Ketturi/LedMatrix/Hardware/Case/IMG_20160126_170815.jpg

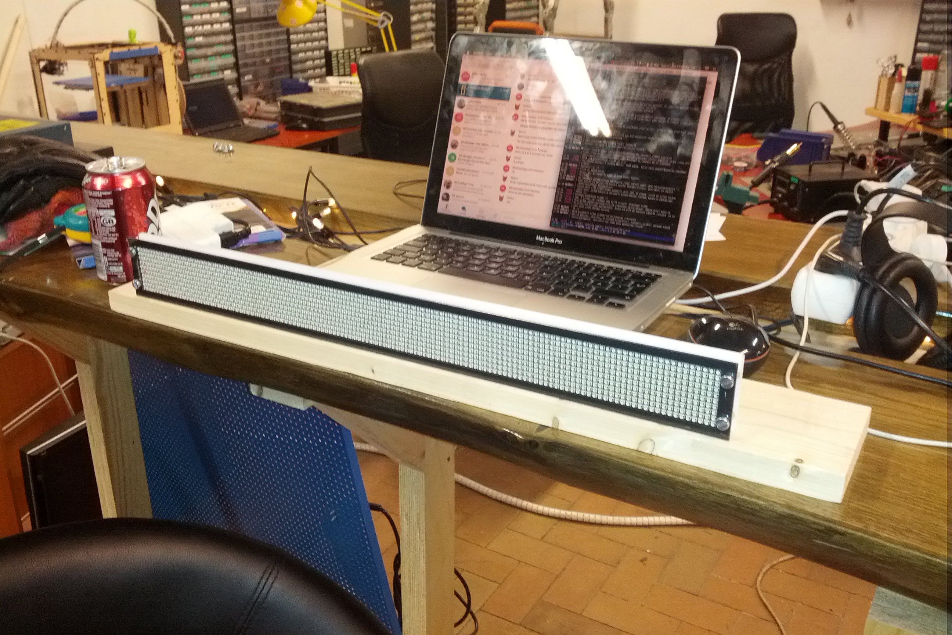
Hardware/Case/IMG_20160126_170815.jpg
