Ketturi/LedMatrix/Hardware/Case/IMG_20160127_182910.jpg

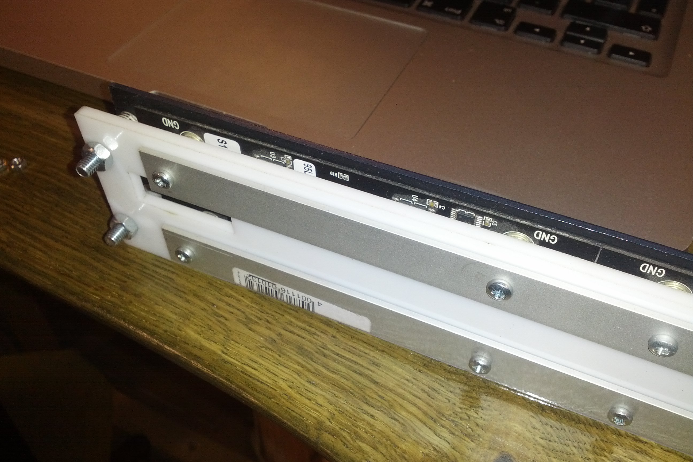
Hardware/Case/IMG_20160127_182910.jpg
