Ketturi/LedMatrix/Hardware/IMG_20160901_110750.jpg

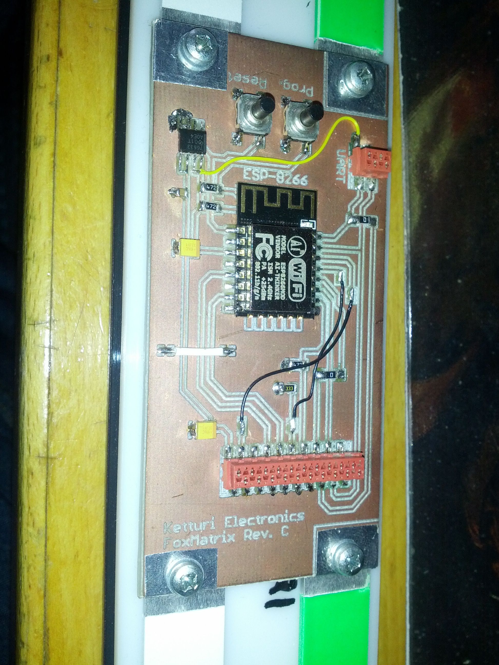
Hardware/IMG_20160901_110750.jpg
