Ketturi/LedMatrix/Arduino source/FoxFont.h

/*
  10 pixels high variable width font for LED matrix display
  created by
  Ketturi Fox 2017

  This work is licensed under a Creative Commons Attribution-ShareAlike 4.0 International License.
  https://creativecommons.org/licenses/by-sa/4.0/
*/

const uint8_t FoxFontBitmaps[] PROGMEM = {
  // Bitmap Data:

  /* 0x20 032 */
  0x80, 0x80, 0x80, 0x80, 0x80, 0x80, 0x00, 0x80, /* 0x21 033 */
  0x90, 0x90, 0x90, /* 0x22 034 */
  0x48, 0x48, 0xFC, 0x48, 0x48, 0xFC, 0x48, 0x48, /* 0x23 035 */
  0x20, 0x70, 0x88, 0x80, 0x70, 0x08, 0x88, 0x70, 0x20, /* 0x24 036 */
  0x42, 0xA4, 0x48, 0x10, 0x24, 0x4A, 0x84, /* 0x25 037 */
  0x30, 0x48, 0x30, 0x4C, 0x88, 0x88, 0x74, /* 0x26 038 */
  0x40, 0x40, 0x80, /* 0x27 039 */
  0x20, 0x40, 0x80, 0x80, 0x80, 0x80, 0x80, 0x80, 0x40, 0x20, /* 0x28 040 */
  0x80, 0x40, 0x20, 0x20, 0x20, 0x20, 0x20, 0x20, 0x40, 0x80, /* 0x29 041 */
  0xA8, 0x70, 0xF8, 0x70, 0xA8, /* 0x2A 042 */
  0x20, 0x20, 0xF8, 0x20, 0x20, /* 0x2B 043 */
  0x40, 0x80, /* 0x2C 044 */
  0xF8, /* 0x2D 045 */
  0x80, /* 0x2E 046 */
  0x04, 0x08, 0x10, 0x20, 0x40, 0x80, /* 0x2F 047 */
  0x70, 0x88, 0x88, 0x88, 0x88, 0x88, 0x88, 0x70, /* 0x30 048 */
  0x40, 0xC0, 0x40, 0x40, 0x40, 0x40, 0x40, 0xE0, /* 0x31 049 */
  0x70, 0x88, 0x08, 0x10, 0x20, 0x40, 0x80, 0xF8, /* 0x32 050 */
  0x70, 0x88, 0x08, 0x30, 0x08, 0x08, 0x88, 0x70, /* 0x33 051 */
  0x08, 0x18, 0x28, 0x48, 0x88, 0xF8, 0x08, 0x08, /* 0x34 052 */
  0xF8, 0x80, 0x80, 0xF0, 0x08, 0x08, 0x88, 0x70, /* 0x35 053 */
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
  { 243, 8, 8, 6, 0, -8 }, /* 0x45 069 */
  { 251, 8, 8, 6, 0, -8 }, /* 0x46 070 */
  { 259, 8, 8, 6, 0, -8 }, /* 0x47 071 */
  { 267, 8, 8, 6, 0, -8 }, /* 0x48 072 */
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
};


const GFXfont FoxFont PROGMEM = {
  (uint8_t  *)FoxFontBitmaps,
  (GFXglyph *)FoxFontGlyphs,
  0x20, 0x7E, 10
};
