Ketturi/LedMatrix/Arduino source/Bitmaps.h

/*
   Static bitmap icons in Adafruit GFX format
   Ketturi Fox 2017

  This work is licensed under a Creative Commons Attribution-ShareAlike 4.0 International License.
  https://creativecommons.org/licenses/by-sa/4.0/
*/
 
 // 'clock'
const unsigned char BitmapClock [] PROGMEM = {
  0x3e, 0x00, 0x41, 0x00, 0x82, 0x80, 0x84, 0x80, 0xb8, 0x80, 0x80, 0x80, 0x80, 0x80, 0x41, 0x00, 
  0x3e, 0x00, 0x00, 0x0
};
 // 'calendar'
const unsigned char BitmapCalendar [] PROGMEM = {
  0x63, 0x00, 0xff, 0x80, 0xff, 0x80, 0x80, 0x80, 0xaa, 0x80, 0x80, 0x80, 0xaa, 0x80, 0x80, 0x80, 
  0xff, 0x80, 0x00, 0x0
};
 // 'info'
const unsigned char BitmapInfo [] PROGMEM = {
  0x3e, 0x00, 0x41, 0x00, 0x88, 0x80, 0x80, 0x80, 0x88, 0x80, 0x88, 0x80, 0x88, 0x80, 0x41, 0x00, 
  0x3e, 0x00, 0x00, 0x0
};
 // 'guestion'
const unsigned char BitmapGuestion [] PROGMEM = {
  0x3e, 0x00, 0x41, 0x00, 0x9c, 0x80, 0x84, 0x80, 0x88, 0x80, 0x80, 0x80, 0x88, 0x80, 0x41, 0x00, 
  0x3e, 0x00, 0x00, 0x0
};
 // 'message'
const unsigned char BitmapMsg [] PROGMEM = {
  0x3e, 0x00, 0x41, 0x00, 0x80, 0x80, 0xaa, 0x80, 0x80, 0x80, 0x41, 0x00, 0x2e, 0x00, 0x30, 0x00, 
  0x20, 0x00, 0x00, 0x0
};
 // 'bus'
const unsigned char BitmapBus [] PROGMEM = {
  0x7f, 0x00, 0xbe, 0x80, 0x80, 0x80, 0x84, 0x80, 0x8e, 0x80, 0xff, 0x80, 0x9c, 0x80, 0xff, 0x80, 
  0x63, 0x00, 0x00, 0x0
};
 // 'email'
const unsigned char BitmapEmail [] PROGMEM = {
  0x00, 0x00, 0xff, 0x80, 0xc1, 0x80, 0xa2, 0x80, 0x94, 0x80, 0x88, 0x80, 0x80, 0x80, 0xff, 0x80, 
  0x00, 0x00, 0x00, 0x0
};
 // 'Warning'
const unsigned char BitmapWarn [] PROGMEM = {
  0x08, 0x00, 0x1c, 0x00, 0x14, 0x00, 0x36, 0x00, 0x36, 0x00, 0x77, 0x00, 0x7f, 0x00, 0xf7, 0x80, 
  0xff, 0x80, 0x00, 0x0
};
 // 'Wifi'
const unsigned char BitmapWifiOn [] PROGMEM = {
  0x00, 0x00, 0x3f, 0x80, 0x40, 0x40, 0x9f, 0x20, 0x20, 0x80, 0x4e, 0x40, 0x11, 0x00, 0x00, 0x00, 
  0x04, 0x00, 0x0e, 0x0
};
 // 'noWifi'
const unsigned char BitmapWifiOff [] PROGMEM = {
  0x00, 0x00, 0x20, 0x80, 0x11, 0x00, 0x0a, 0x00, 0x04, 0x00, 0x0a, 0x00, 0x11, 0x00, 0x20, 0x80, 
  0x04, 0x00, 0x0e, 0x0
};
 // 'IP'
const unsigned char BitmapIP [] PROGMEM = {
  0xb0, 0x00, 0xa8, 0x00, 0xb0, 0x00, 0xa0, 0x00, 0x00, 0x00, 0x4c, 0xc0, 0xaa, 0xa0, 0xea, 0xc0, 
  0xac, 0xa0, 0x00, 0x0
};
 // 'MAC'
const unsigned char BitmapMAC [] PROGMEM = {
  0xe4, 0x60, 0xea, 0x80, 0xae, 0x80, 0xaa, 0x60, 0x00, 0x00, 0x4c, 0xc0, 0xaa, 0xa0, 0xea, 0xc0, 
  0xac, 0xa0, 0x00, 0x0
};
 // 'AP'
const unsigned char BitmapAP [] PROGMEM = {
  0x4c, 0x00, 0xaa, 0x00, 0xec, 0x00, 0xa8, 0x00, 0x00, 0x00, 0xee, 0x40, 0xc4, 0xa0, 0x24, 0xe0, 
  0xe4, 0xa0, 0x00, 0x0
};
